gabrieltintu/OpenBook/Images/3D_PCB_2.png

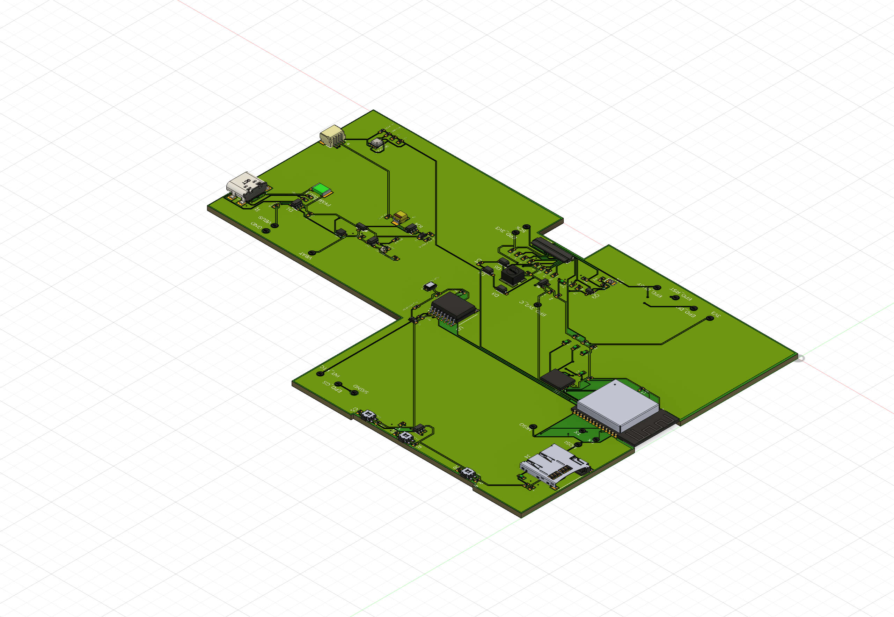
Images/3D_PCB_2.png
