gabrieltintu/OpenBook/Images/3D_PCB_3.png

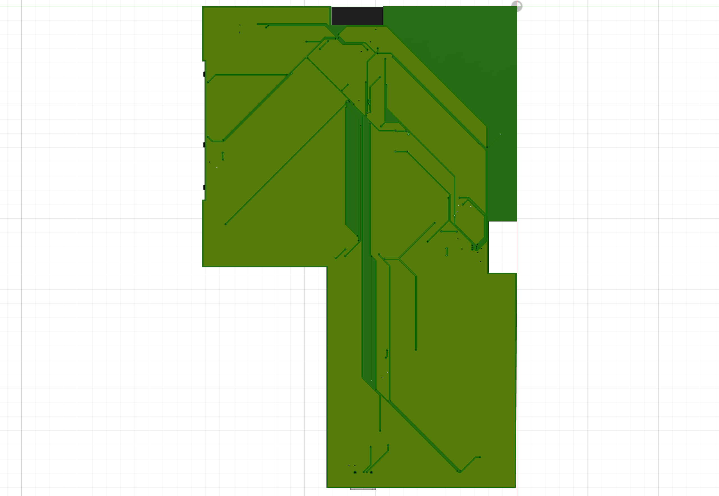
Images/3D_PCB_3.png
