gabrieltintu/OpenBook/Images/BATTERY_3.png

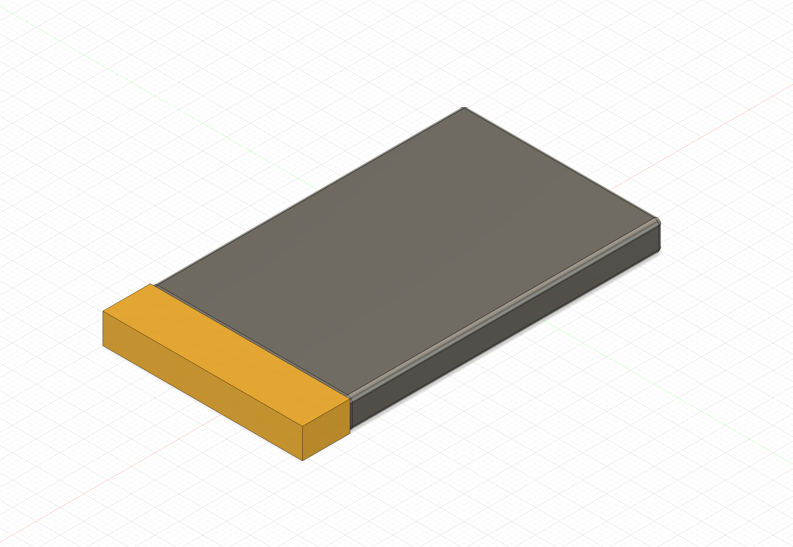
Images/BATTERY_3.png
